ETML-ES-SLO/TOTEM_ES/soft/TestTotem/firmware/src/system_config/default/system_init.c

/*******************************************************************************
  System Initialization File

  File Name:
    system_init.c

  Summary:
    This file contains source code necessary to initialize the system.

  Description:
    This file contains source code necessary to initialize the system.  It
    implements the "SYS_Initialize" function, defines the configuration bits,
    and allocates any necessary global system resources, such as the
    sysObj structure that contains the object handles to all the MPLAB Harmony
    module objects in the system.
 *******************************************************************************/

// DOM-IGNORE-BEGIN
/*******************************************************************************
Copyright (c) 2013-2015 released Microchip Technology Inc.  All rights reserved.

Microchip licenses to you the right to use, modify, copy and distribute
Software only when embedded on a Microchip microcontroller or digital signal
controller that is integrated into your product or third party product
(pursuant to the sublicense terms in the accompanying license agreement).

You should refer to the license agreement accompanying this Software for
additional information regarding your rights and obligations.

SOFTWARE AND DOCUMENTATION ARE PROVIDED AS IS WITHOUT WARRANTY OF ANY KIND,
EITHER EXPRESS OR IMPLIED, INCLUDING WITHOUT LIMITATION, ANY WARRANTY OF
MERCHANTABILITY, TITLE, NON-INFRINGEMENT AND FITNESS FOR A PARTICULAR PURPOSE.
IN NO EVENT SHALL MICROCHIP OR ITS LICENSORS BE LIABLE OR OBLIGATED UNDER
CONTRACT, NEGLIGENCE, STRICT LIABILITY, CONTRIBUTION, BREACH OF WARRANTY, OR
OTHER LEGAL EQUITABLE THEORY ANY DIRECT OR INDIRECT DAMAGES OR EXPENSES
INCLUDING BUT NOT LIMITED TO ANY INCIDENTAL, SPECIAL, INDIRECT, PUNITIVE OR
CONSEQUENTIAL DAMAGES, LOST PROFITS OR LOST DATA, COST OF PROCUREMENT OF
SUBSTITUTE GOODS, TECHNOLOGY, SERVICES, OR ANY CLAIMS BY THIRD PARTIES
(INCLUDING BUT NOT LIMITED TO ANY DEFENSE THEREOF), OR OTHER SIMILAR COSTS.
 *******************************************************************************/
// DOM-IGNORE-END

// *****************************************************************************
// *****************************************************************************
// Section: Included Files
// *****************************************************************************
// *****************************************************************************

#include "system_config.h"
#include "system_definitions.h"


// ****************************************************************************
// ****************************************************************************
// Section: Configuration Bits
// ****************************************************************************
// ****************************************************************************
// <editor-fold defaultstate="collapsed" desc="Configuration Bits">

/*** DEVCFG0 ***/

#pragma config DEBUG =      OFF
#pragma config JTAGEN =     OFF
#pragma config ICESEL =     ICS_PGx1
#pragma config PWP =        OFF
#pragma config BWP =        OFF
#pragma config CP =         OFF

/*** DEVCFG1 ***/

#pragma config FNOSC =      FRCPLL
#pragma config FSOSCEN =    OFF
#pragma config IESO =       OFF
#pragma config POSCMOD =    OFF
#pragma config OSCIOFNC =   OFF
#pragma config FPBDIV =     DIV_1
#pragma config FCKSM =      CSDCMD
#pragma config WDTPS =      PS1048576
#pragma config FWDTEN =     OFF
#pragma config WINDIS =     OFF
#pragma config FWDTWINSZ =  WINSZ_50
/*** DEVCFG2 ***/

#pragma config FPLLIDIV =   DIV_2
#pragma config FPLLMUL =    MUL_24
#pragma config FPLLODIV =   DIV_2
/*** DEVCFG3 ***/

#pragma config USERID =     0xffff
#pragma config PMDL1WAY =   ON
#pragma config IOL1WAY =    ON
// </editor-fold>

// *****************************************************************************
// *****************************************************************************
// Section: Driver Initialization Data
// *****************************************************************************
// *****************************************************************************
// <editor-fold defaultstate="collapsed" desc="DRV_SPI Initialization Data"> 
 /*** SPI Driver Initialization Data ***/
// </editor-fold>
// <editor-fold defaultstate="collapsed" desc="DRV_Timer Initialization Data">
// </editor-fold>

// *****************************************************************************
// *****************************************************************************
// Section: System Data
// *****************************************************************************
// *****************************************************************************

/* Structure to hold the object handles for the modules in the system. */
SYSTEM_OBJECTS sysObj;

// *****************************************************************************
// *****************************************************************************
// Section: Module Initialization Data
// *****************************************************************************
// *****************************************************************************

// *****************************************************************************
// *****************************************************************************
// Section: Library/Stack Initialization Data
// *****************************************************************************
// *****************************************************************************

// *****************************************************************************
// *****************************************************************************
// Section: System Initialization
// *****************************************************************************
// *****************************************************************************

/*******************************************************************************
  Function:
    void SYS_Initialize ( void *data )

  Summary:
    Initializes the board, services, drivers, application and other modules.

  Remarks:
    See prototype in system/common/sys_module.h.
 */

void SYS_Initialize ( void* data )
{
    /* Core Processor Initialization */
    SYS_CLK_Initialize( NULL );
    SYS_DEVCON_Initialize(SYS_DEVCON_INDEX_0, (SYS_MODULE_INIT*)NULL);
    SYS_DEVCON_PerformanceConfig(SYS_CLK_SystemFrequencyGet());
    SYS_PORTS_Initialize();

    /* Initialize Drivers */

    /* Initialize ADC */
    DRV_ADC_Initialize();


    /*** SPI Driver Index 0 initialization***/

    SYS_INT_VectorPrioritySet(INT_VECTOR_SPI2, INT_PRIORITY_LEVEL7);
    SYS_INT_VectorSubprioritySet(INT_VECTOR_SPI2, INT_SUBPRIORITY_LEVEL0);
    sysObj.spiObjectIdx0 = DRV_SPI_Initialize(DRV_SPI_INDEX_0, (const SYS_MODULE_INIT  * const)NULL);
    /*Initialize TMR0 */
    DRV_TMR0_Initialize();
 
 
    /* Initialize System Services */

    /*** Interrupt Service Initialization Code ***/
    SYS_INT_Initialize();

    /* Initialize Middleware */

    /* Enable Global Interrupts */
    SYS_INT_Enable();

    /* Initialize the Application */
    APP_Initialize();
}


/*******************************************************************************
 End of File
*/
