ETML-ES-SLO/TOTEM_ES/soft/TestTotem/firmware/src/Anim.h

#ifndef Anim_H
#define Anim_H
/* ************************************************************************** */
/** Descriptive File Name
 * autor: Nicolas Fürst
 */
/* ************************************************************************** */


#include <stdint.h>

//Prototype

void Nyan(colorStruct* matrixColor);
bool Text (char* charChain,colorStruct color,colorStruct* matrixColor,bool rainbow);
void Battery (colorStruct* matrixColor);
#endif
