ETML-ES-SLO/TOTEM_ES/soft/TestTotem/firmware/src/Mc32SpiUtil.h

#ifndef Mc32SpiUtil_H
#define Mc32SpiUtil_H
/*--------------------------------------------------------*/
// Mc32SpiUtil.h
/*--------------------------------------------------------*/
//	Description :	Utilitaire gestion SPI CCS like
//
//	Auteur 		: 	C. Huber
//	Version		:	V1.1
//	Compilateur	:	XC32 V1.40
//
/*--------------------------------------------------------*/



#include <stdint.h>


// prototypes des fonctions
void spi_write1( uint8_t Val);
void WriteToLED();
void Led_Set(void);
uint8_t spi_read1( uint8_t Val);
uint8_t spi_read2( uint8_t Val);

#endif
