ETML-ES-SLO/TOTEM_ES/soft/TestTotem/firmware/src/caracLib.h

#ifndef caracLib_H
#define caracLib_H
/* ************************************************************************** */
/** Descriptive File Name
 * autor: Nicolas Fürst
 */
/* ************************************************************************** */


#include <stdint.h>

//Prototype

void ConvertChar (colorStruct *Convert,char character,colorStruct color);

#endif
